lukaso25/USBAudioADDA/photo prototype/02 top.JPG

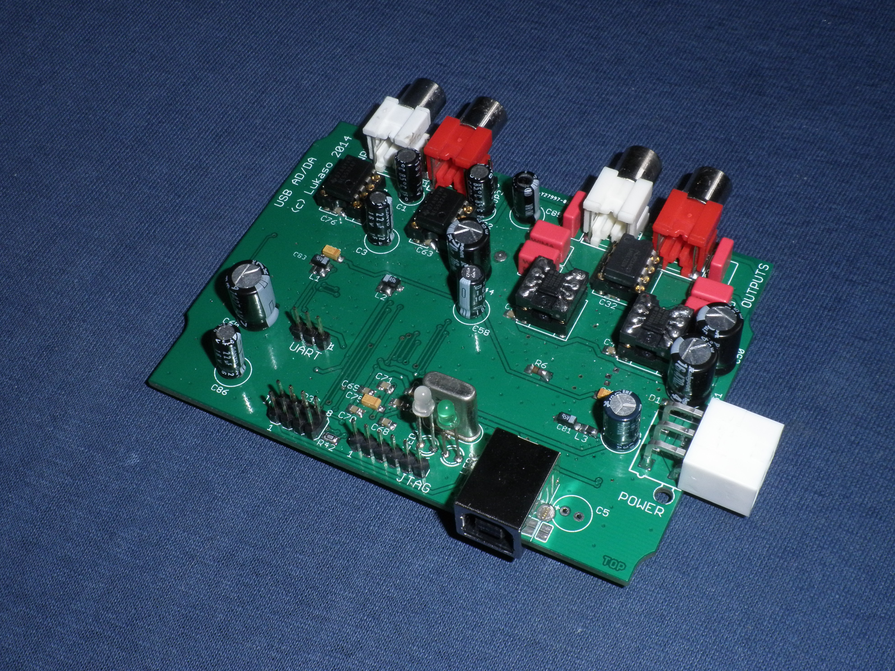
photo prototype/02 top.JPG
