lukaso25/USBAudioADDA/measurements/loopbackARTA1853&1871@44100.png

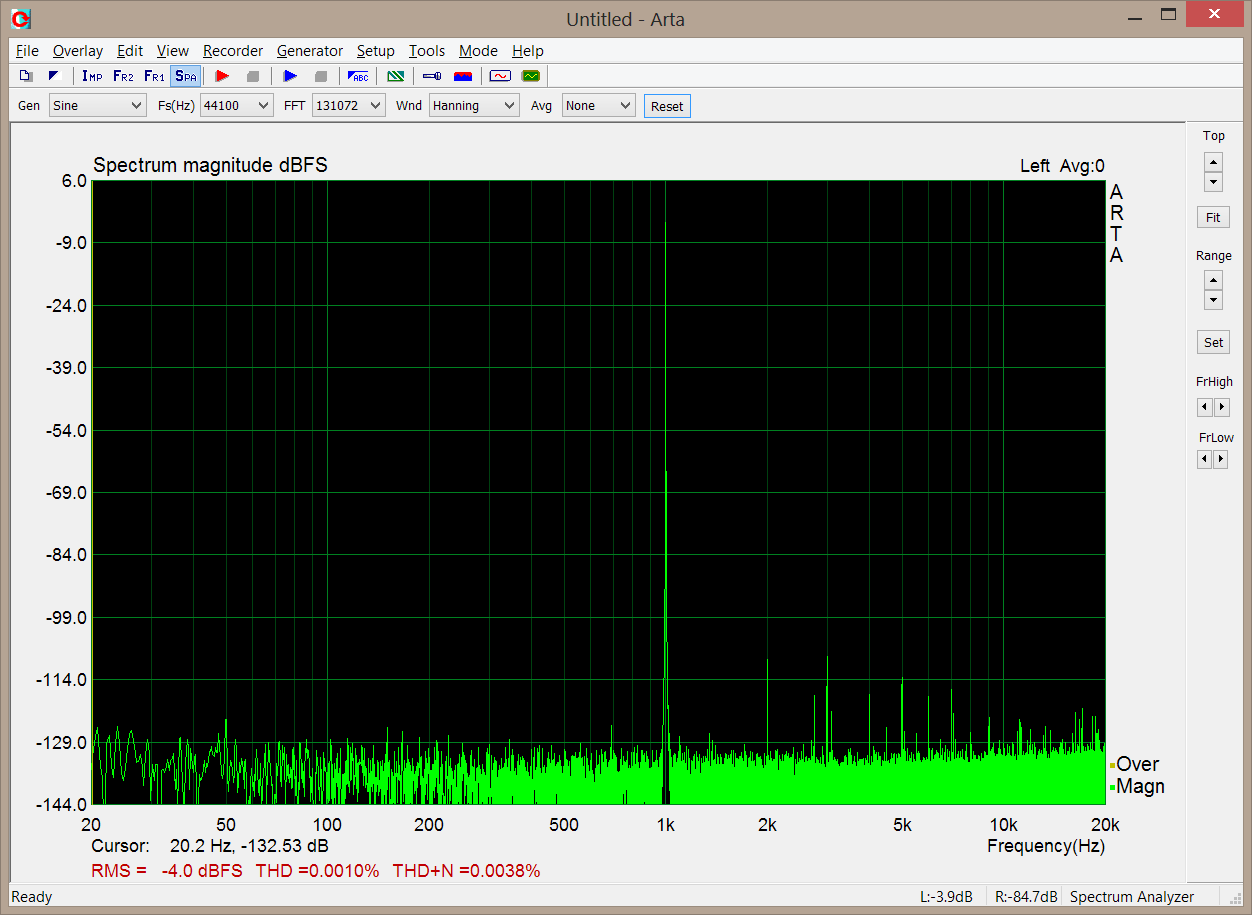
measurements/loopbackARTA1853&1871@44100.png
